Haghighatbin/LucidSens/Images/IMG_0358.jpg

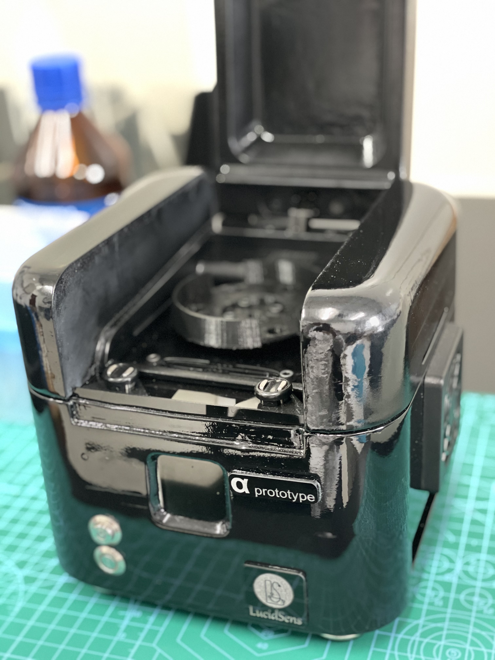
Images/IMG_0358.jpg
