Haghighatbin/LucidSens/Images/IMG_0595.jpg

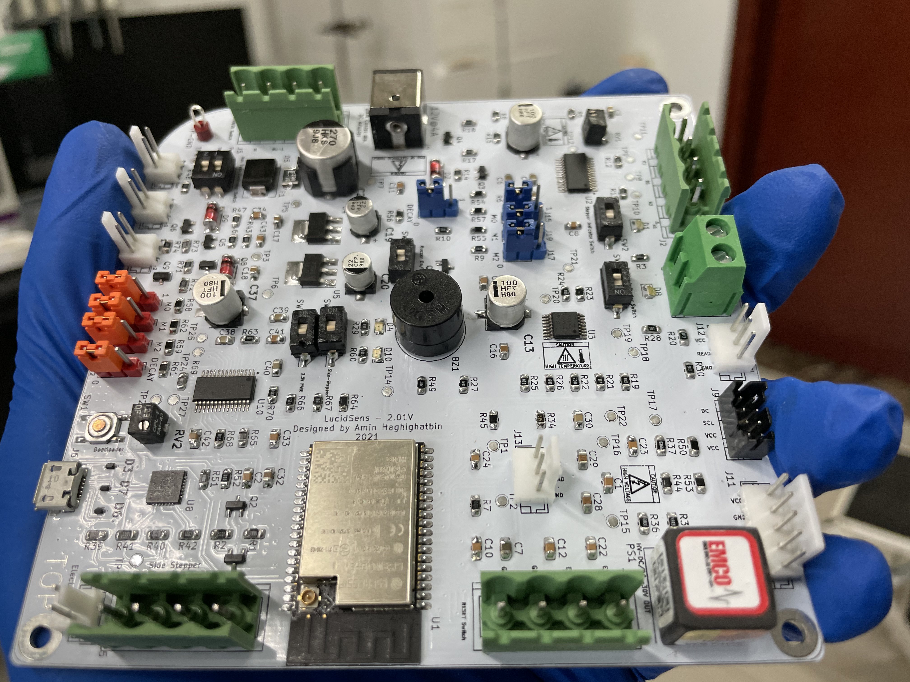
Images/IMG_0595.jpg
