Haghighatbin/LucidSens/Images/IMG_0702.JPG

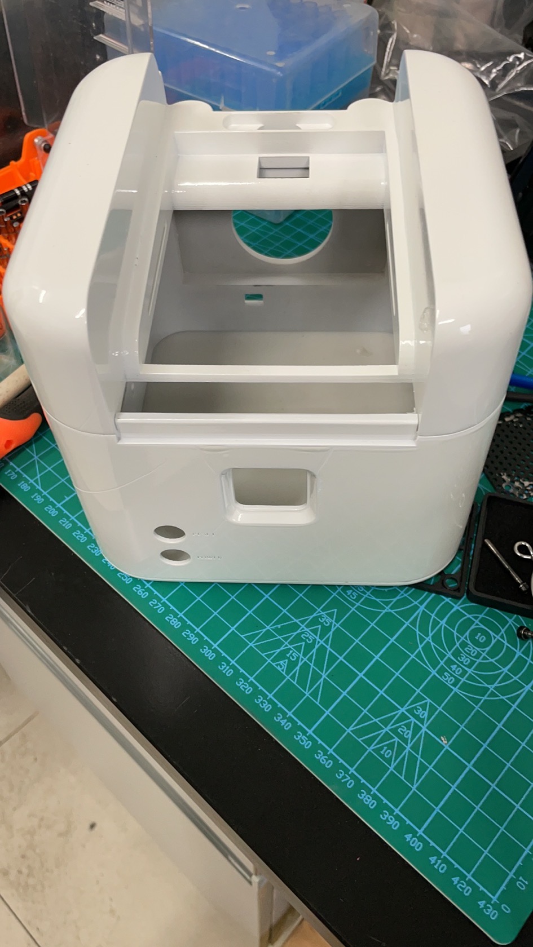
Images/IMG_0702.JPG
