Haghighatbin/LucidSens/Images/IMG_0709.jpg

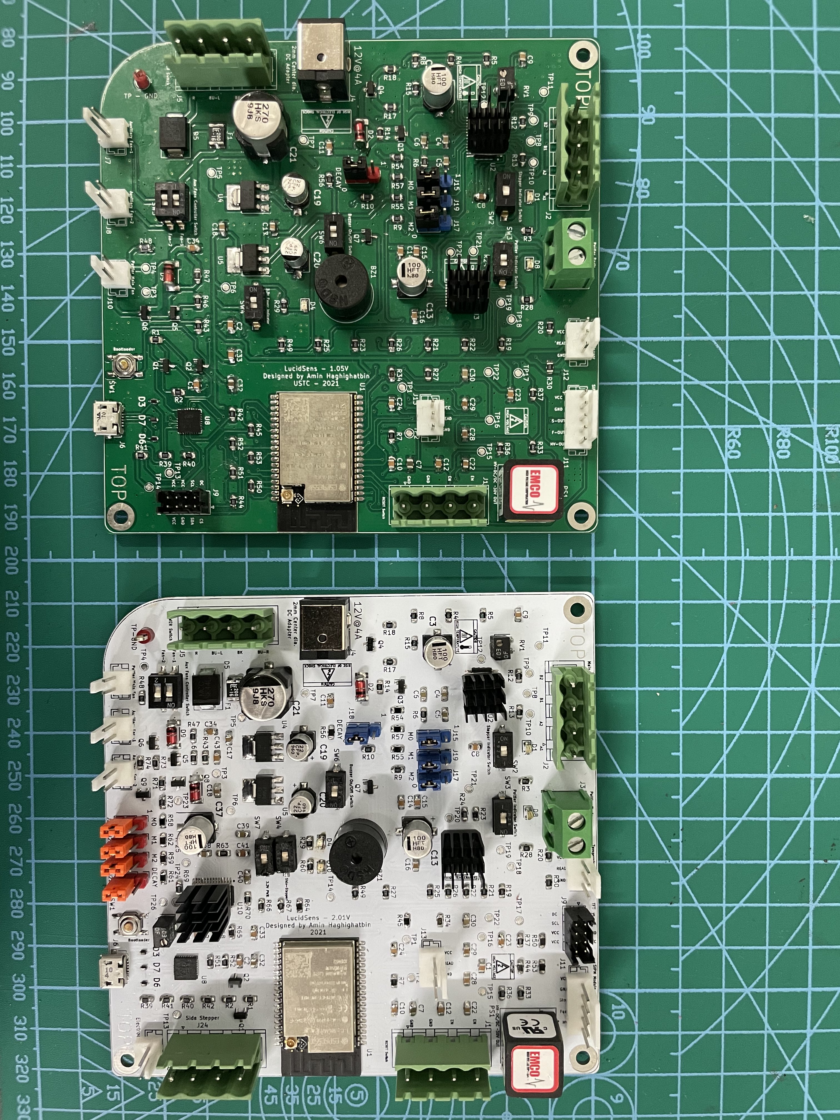
Images/IMG_0709.jpg
