Haghighatbin/LucidSens/Images/IMG_0712.jpg

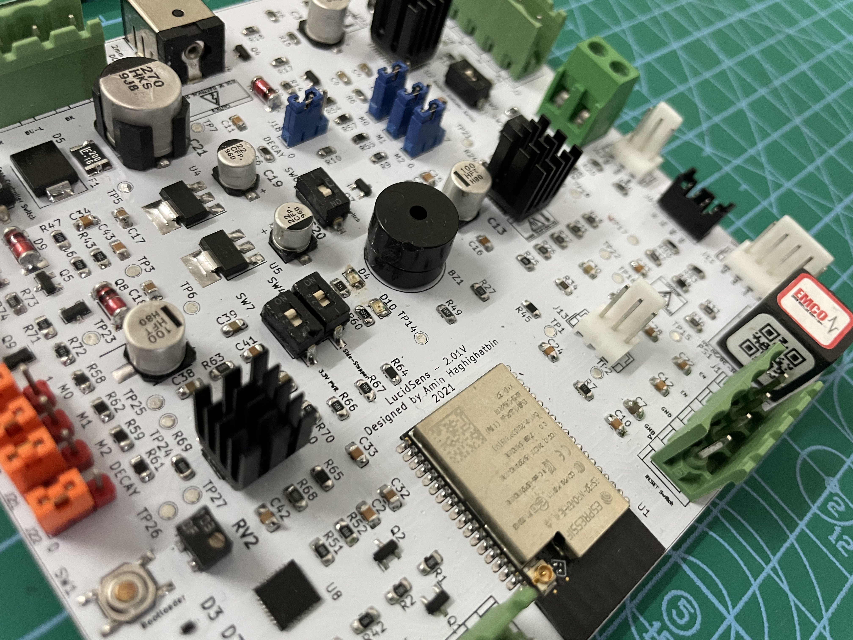
Images/IMG_0712.jpg
