Haghighatbin/LucidSens/Images/IMG_0715.jpg

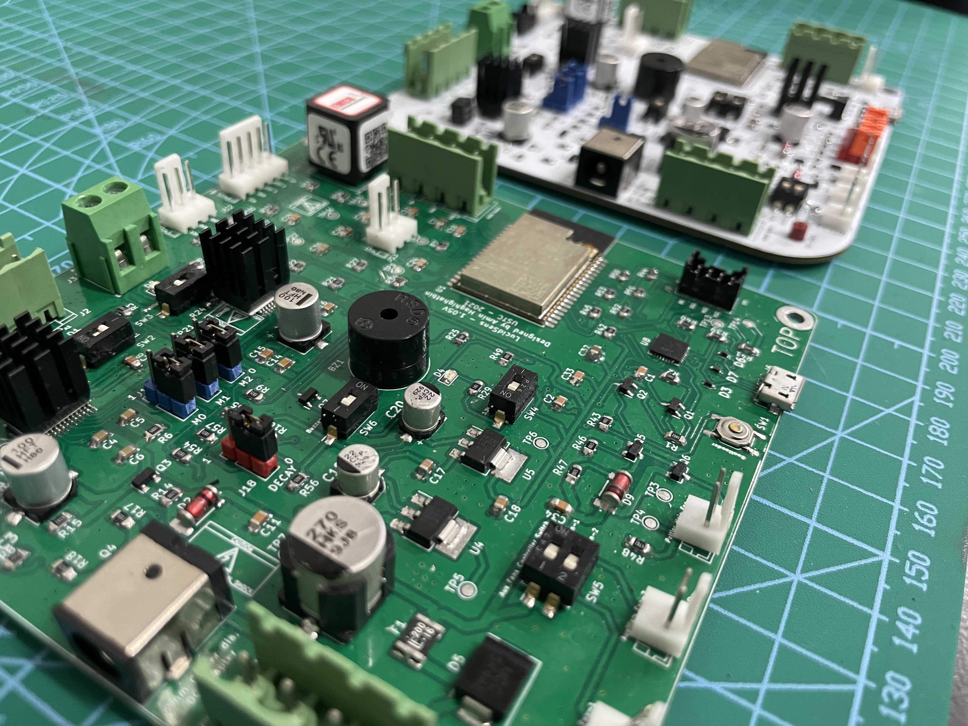
Images/IMG_0715.jpg
