Haghighatbin/LucidSens/Images/IMG_2450.jpg

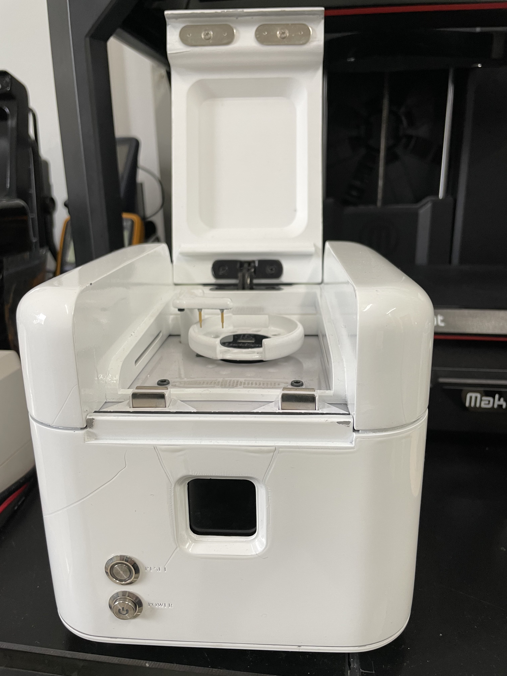
Images/IMG_2450.jpg
