Haghighatbin/LucidSens/Images/IMG_2451.jpg

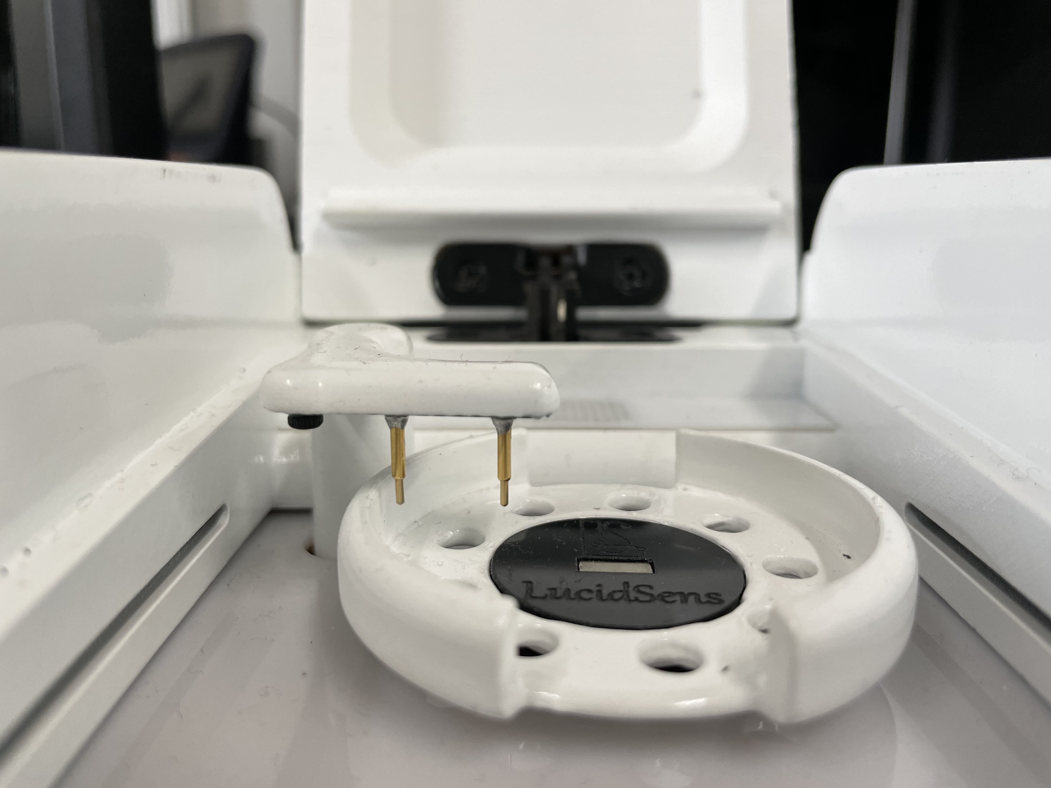
Images/IMG_2451.jpg
