Haghighatbin/LucidSens/Images/IMG_2452.jpg

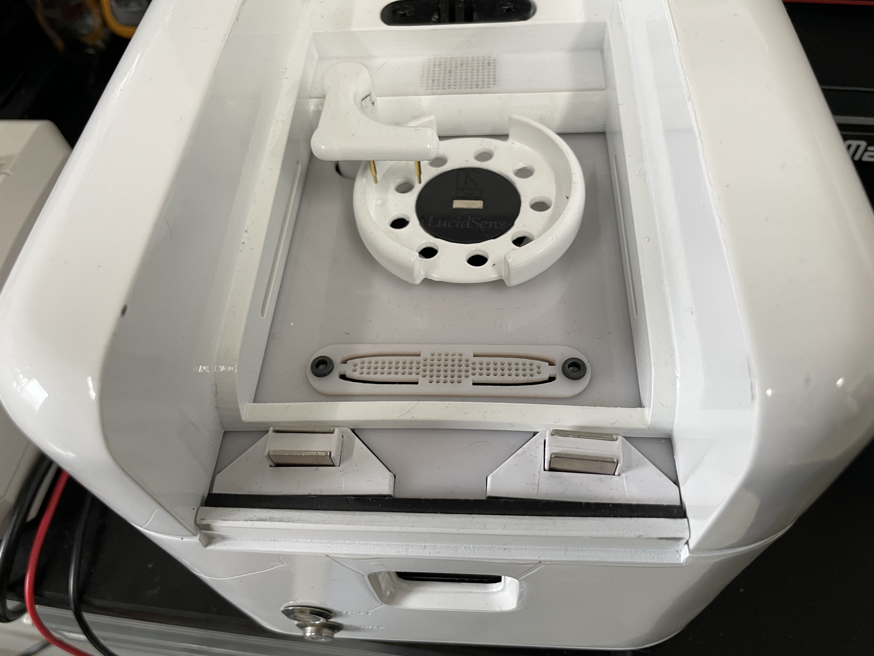
Images/IMG_2452.jpg
