Haghighatbin/LucidSens/Images/IMG_2453.jpg

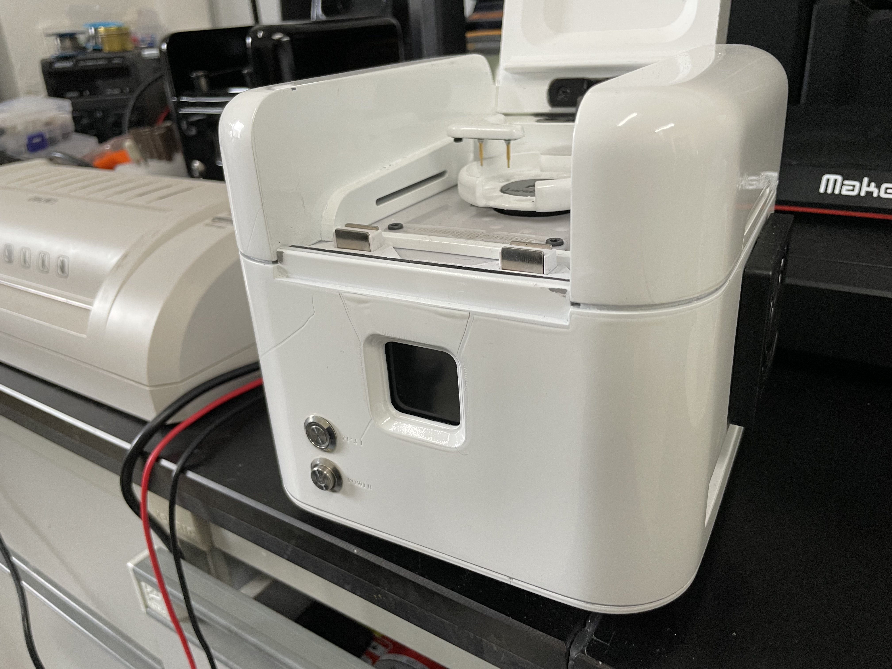
Images/IMG_2453.jpg
