Haghighatbin/LucidSens/Images/IMG_2455.jpg

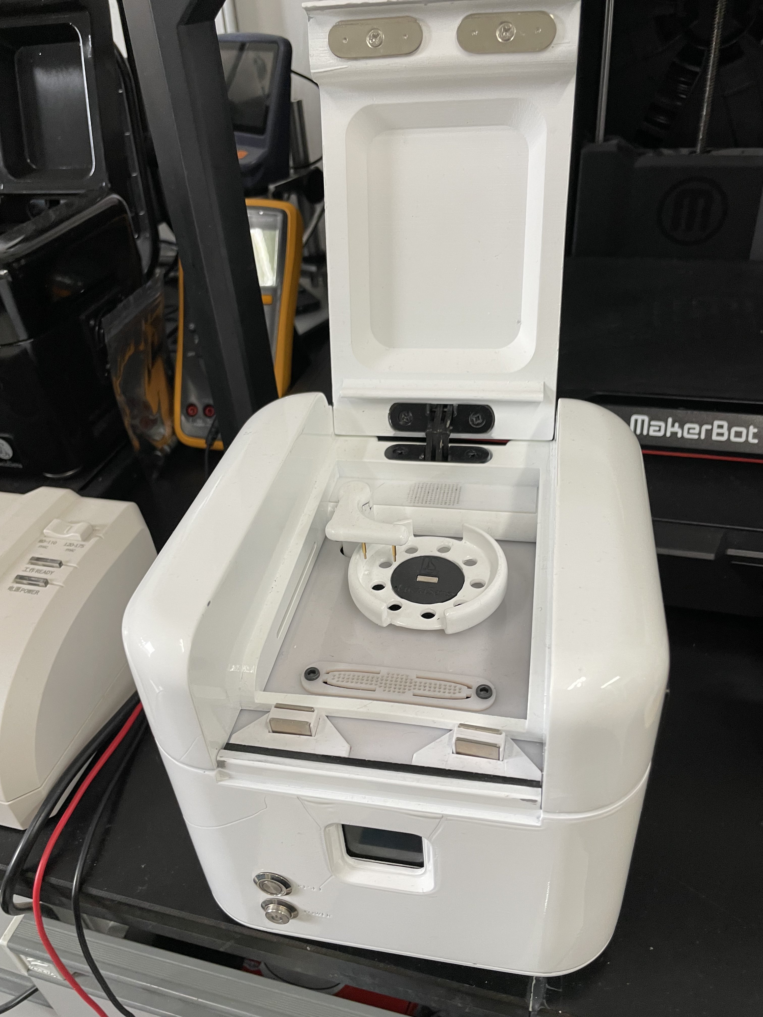
Images/IMG_2455.jpg
