Haghighatbin/LucidSens/Images/IMG_2456.jpg

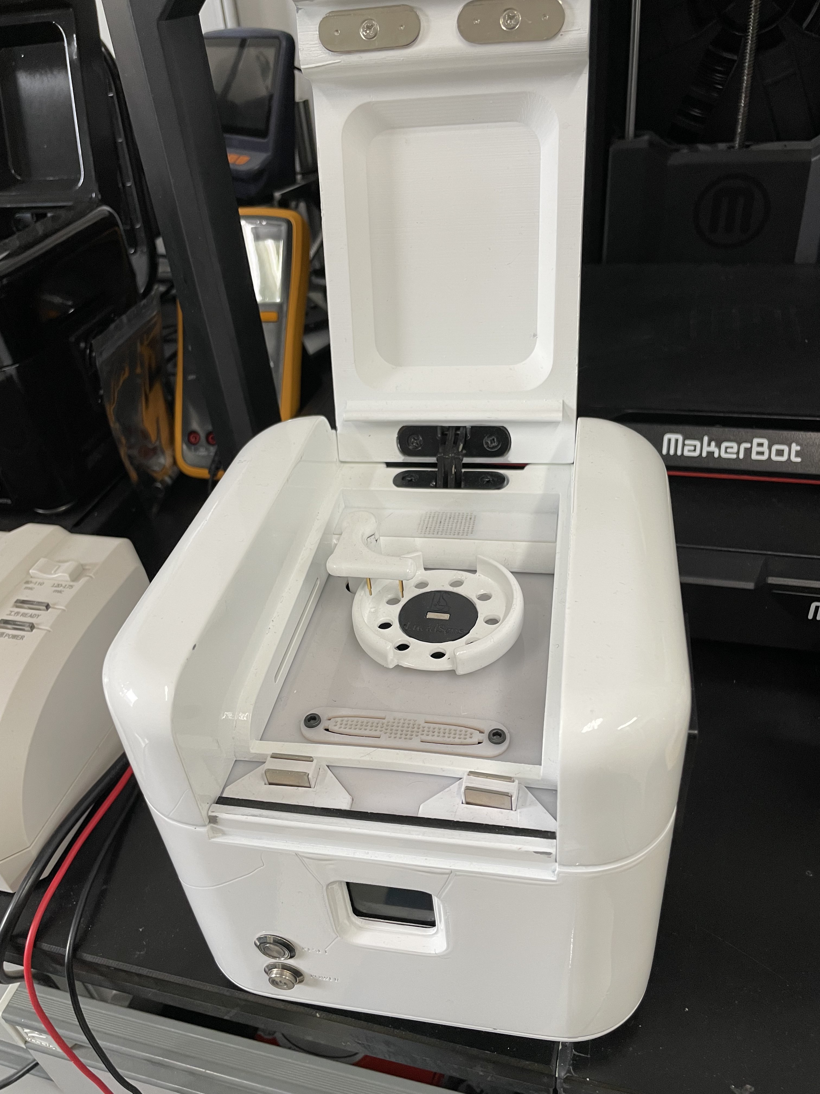
Images/IMG_2456.jpg
