Haghighatbin/LucidSens/Images/IMG_2458.jpg

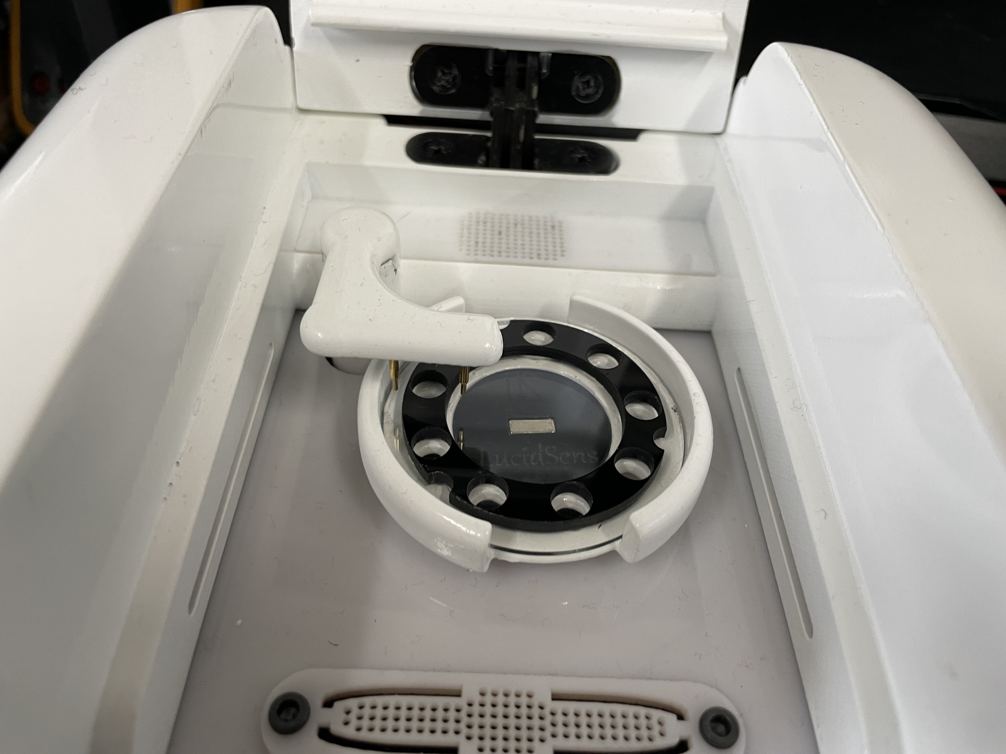
Images/IMG_2458.jpg
