Haghighatbin/LucidSens/Images/IMG_2459.jpg

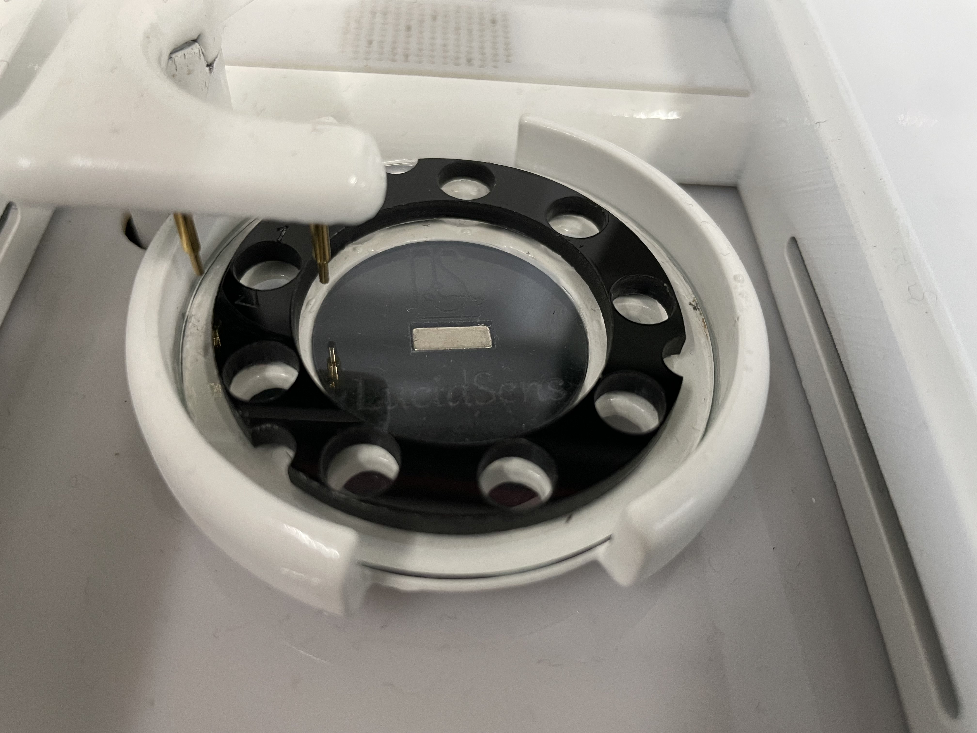
Images/IMG_2459.jpg
