Haghighatbin/LucidSens/Images/IMG_2460.jpg

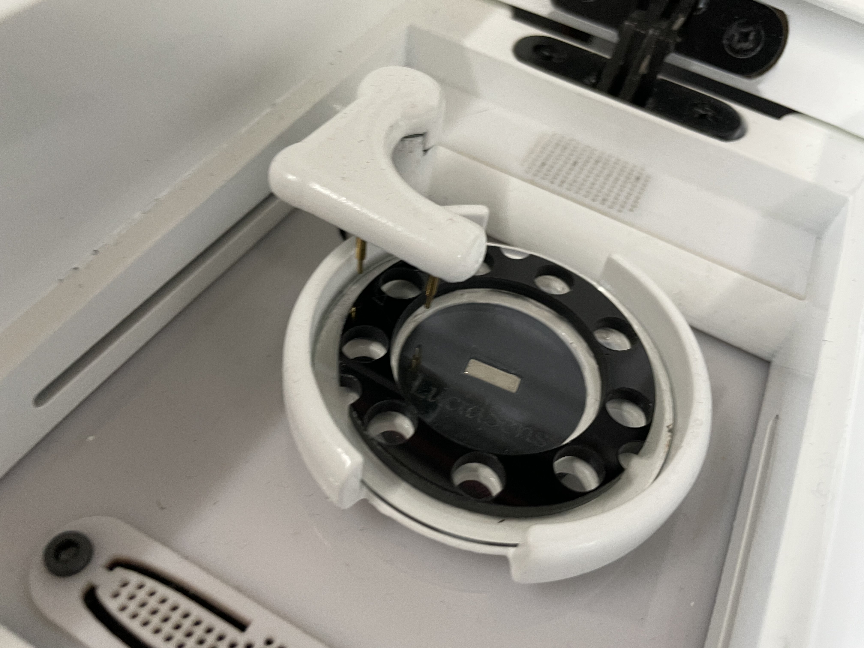
Images/IMG_2460.jpg
