Haghighatbin/LucidSens/Images/IMG_2461.jpg

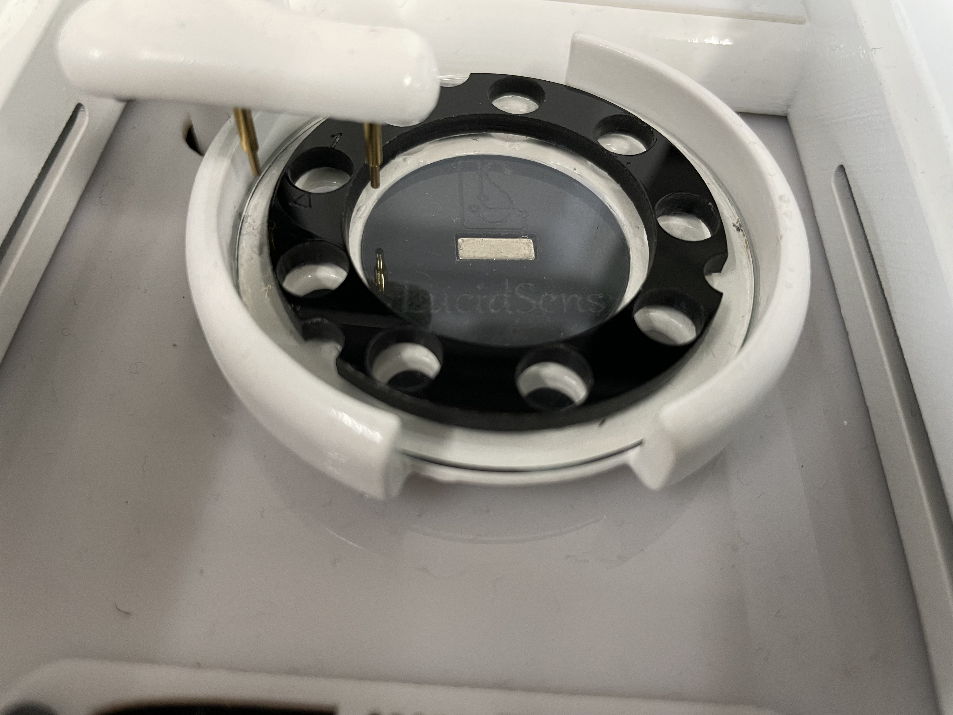
Images/IMG_2461.jpg
