Haghighatbin/LucidSens/Images/IMG_2462.jpg

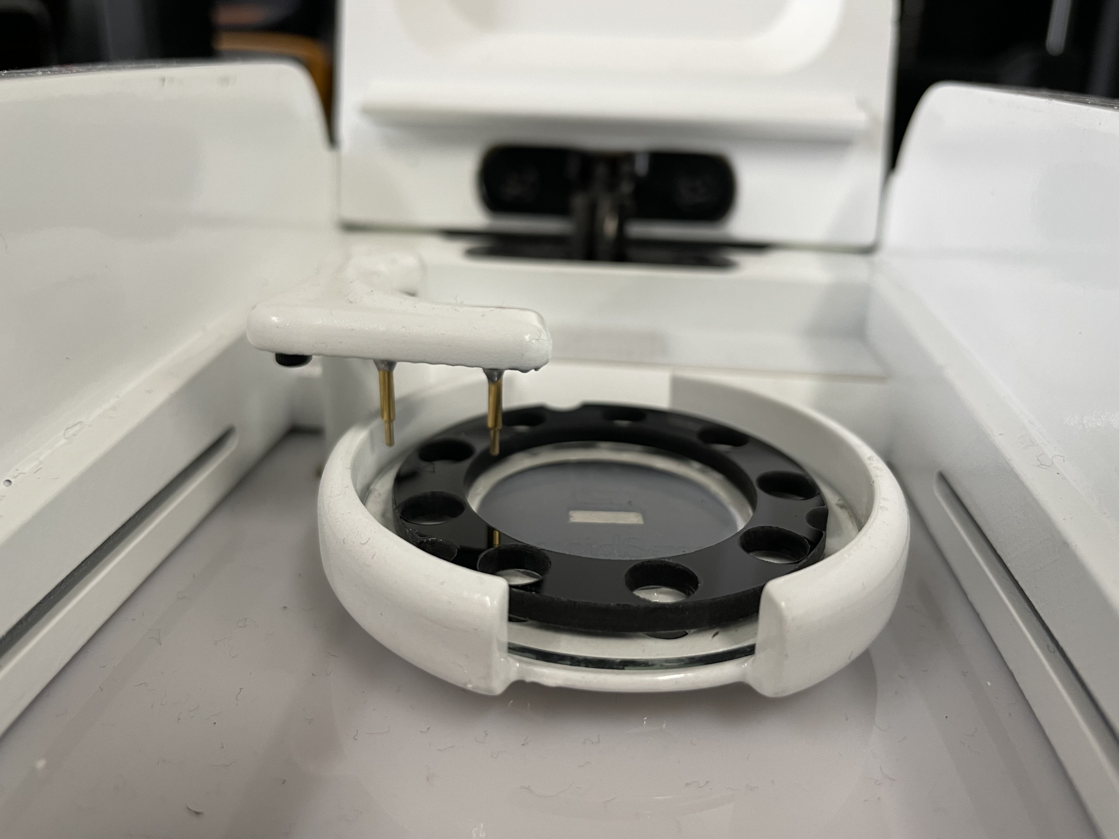
Images/IMG_2462.jpg
