Haghighatbin/LucidSens/Images/IMG_2463.jpg

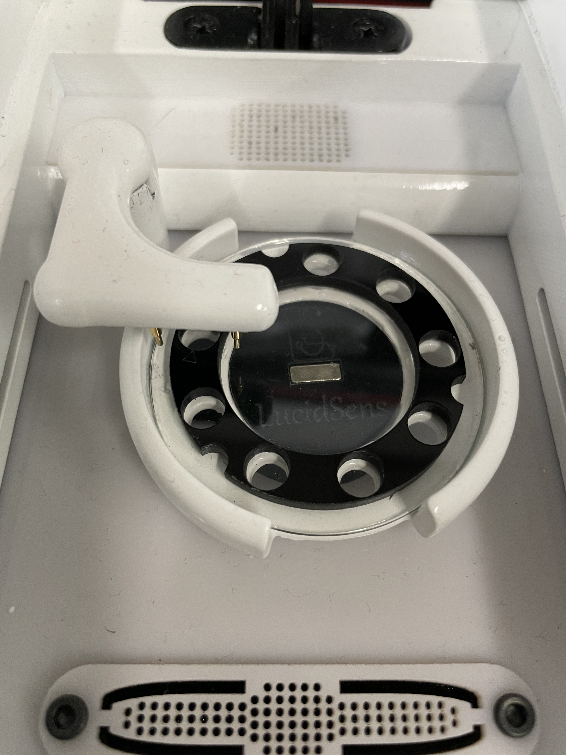
Images/IMG_2463.jpg
