Haghighatbin/LucidSens/Images/IMG_2464.jpg

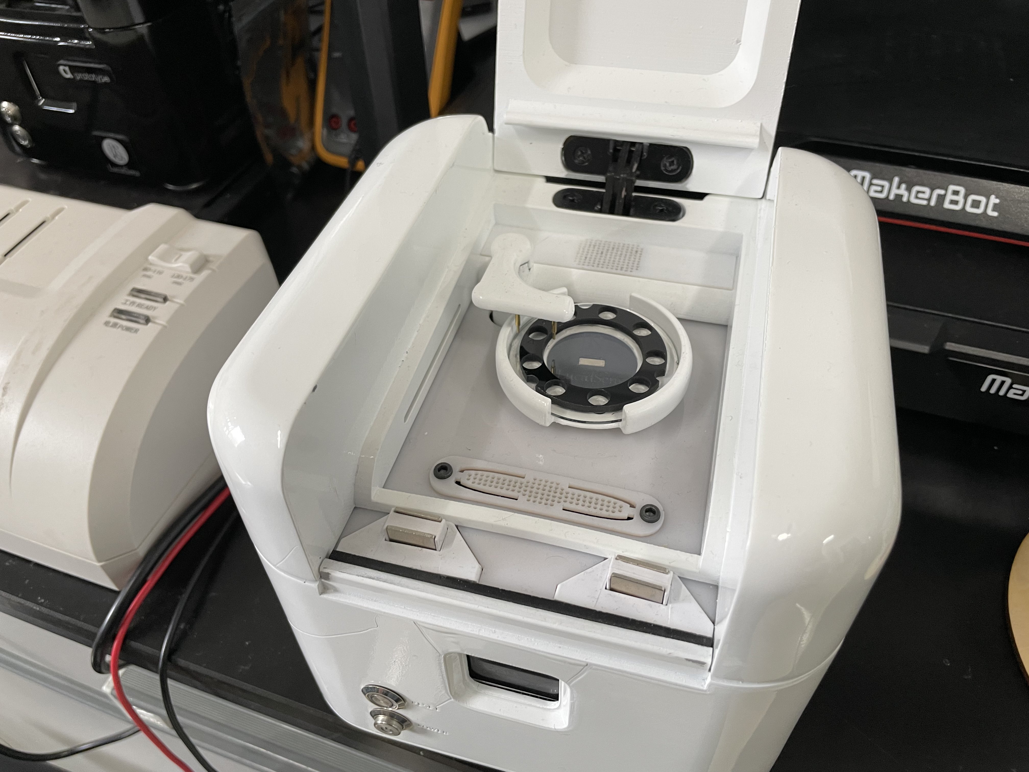
Images/IMG_2464.jpg
