Haghighatbin/LucidSens/Images/IMG_2465.jpg

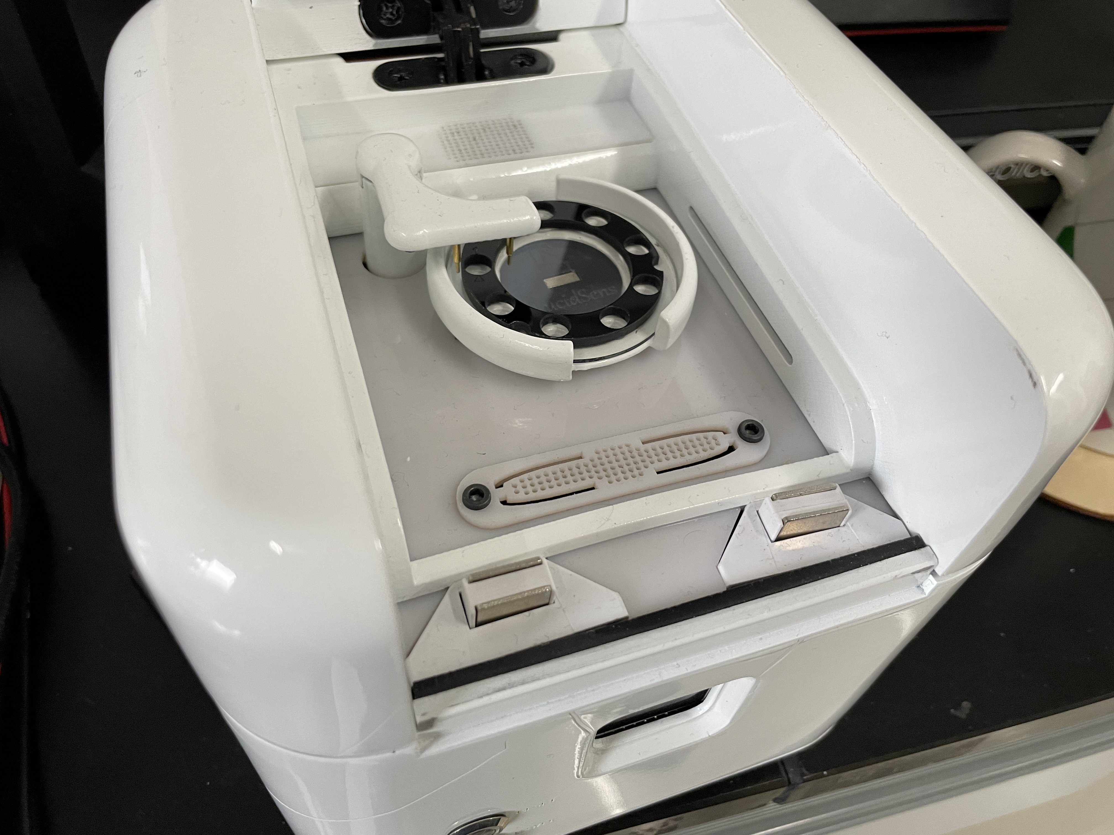
Images/IMG_2465.jpg
