Haghighatbin/LucidSens/Images/IMG_2466.jpg

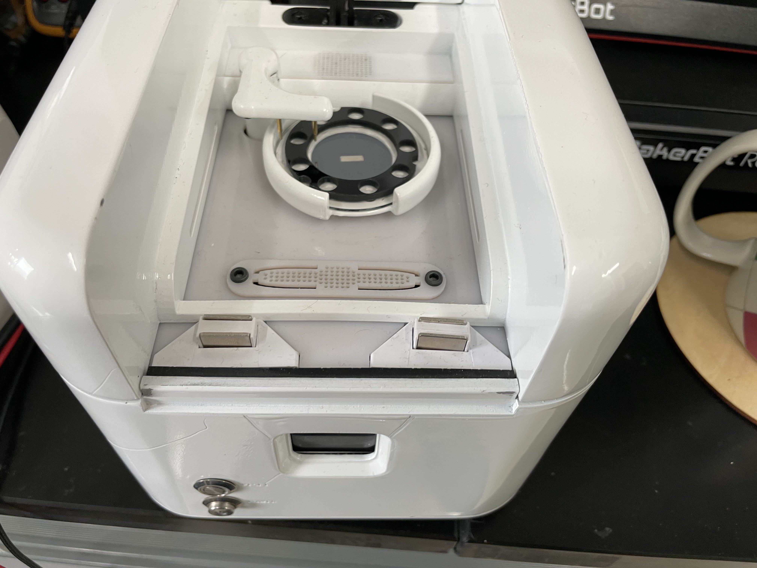
Images/IMG_2466.jpg
