Haghighatbin/LucidSens/Images/IMG_2468.jpg

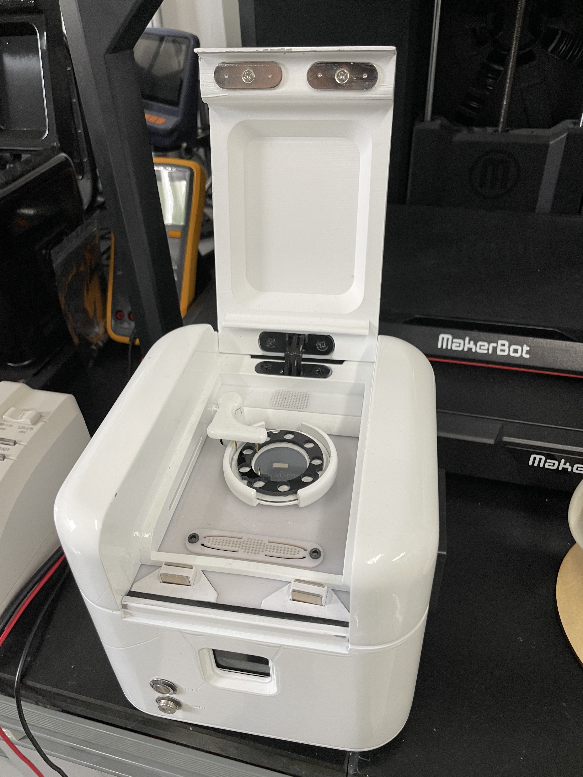
Images/IMG_2468.jpg
