Haghighatbin/LucidSens/Images/IMG_2470.jpg

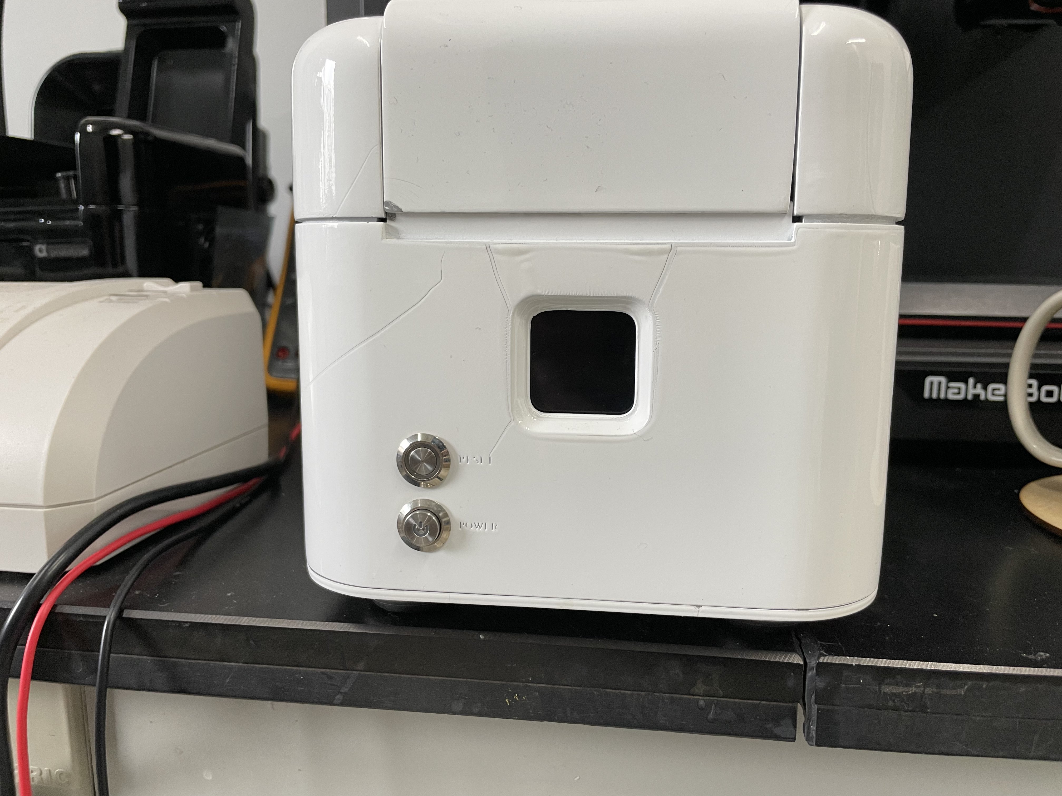
Images/IMG_2470.jpg
