Haghighatbin/LucidSens/Images/IMG_2471.jpg

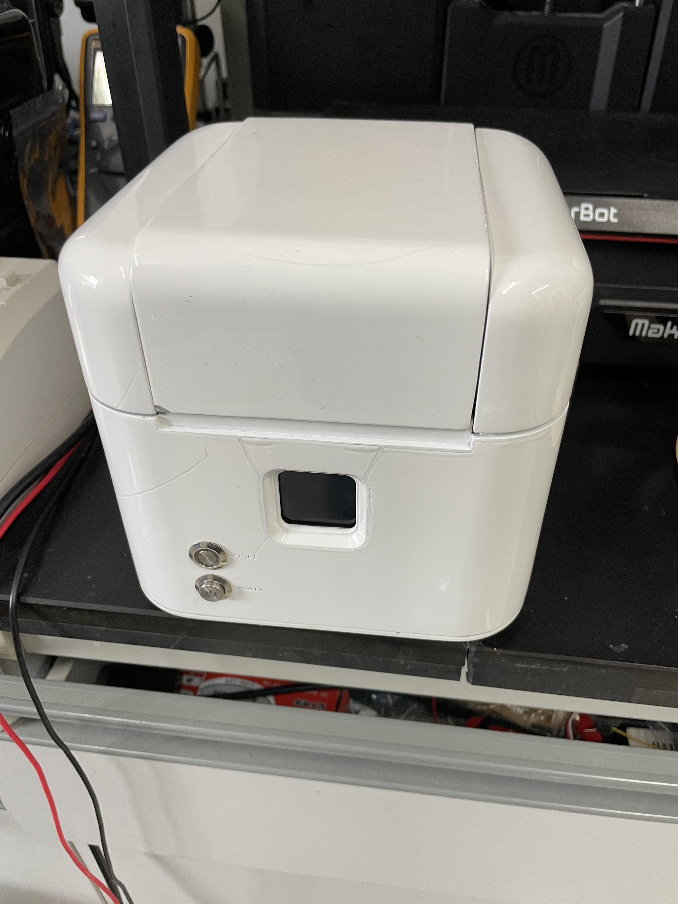
Images/IMG_2471.jpg
