Haghighatbin/LucidSens/Images/IMG_2472.jpg

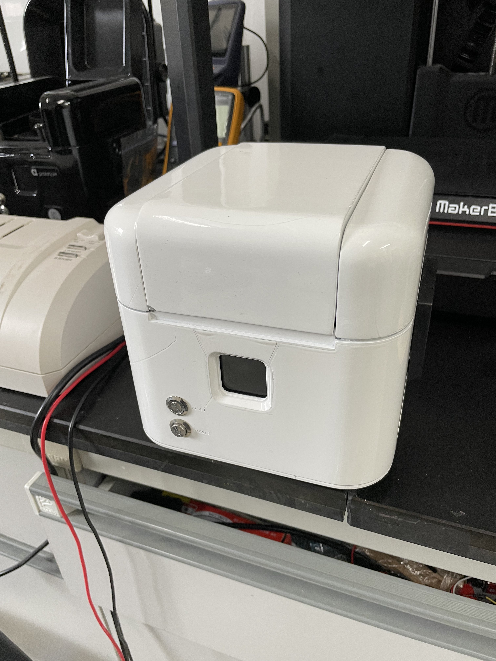
Images/IMG_2472.jpg
