Haghighatbin/LucidSens/Images/IMG_2476.jpg

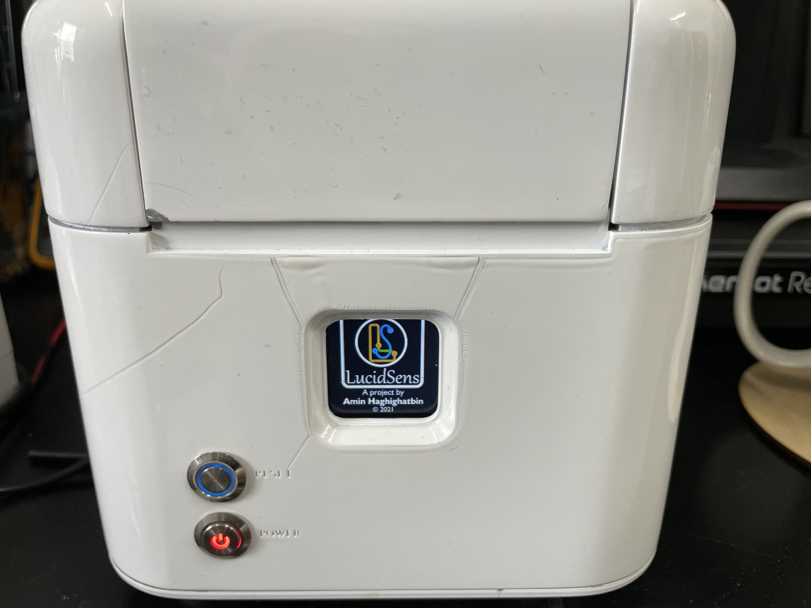
Images/IMG_2476.jpg
