Haghighatbin/LucidSens/Images/IMG_2478.jpg

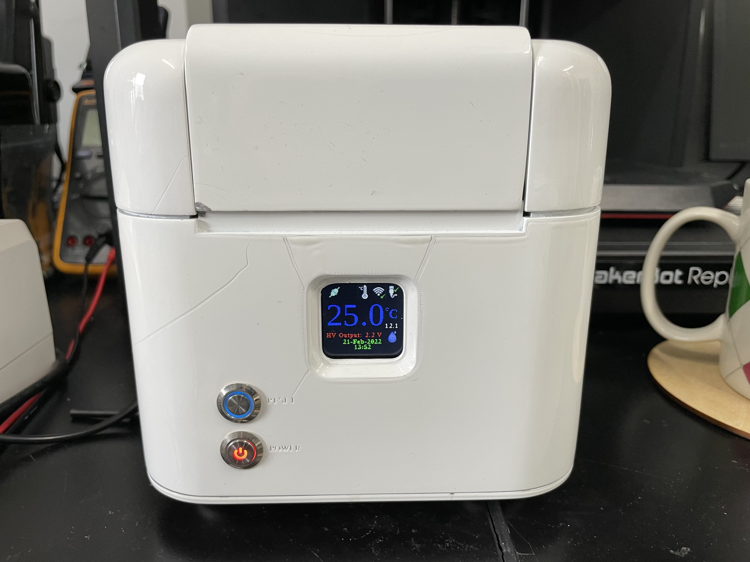
Images/IMG_2478.jpg
