Haghighatbin/LucidSens/Images/IMG_5526.JPG

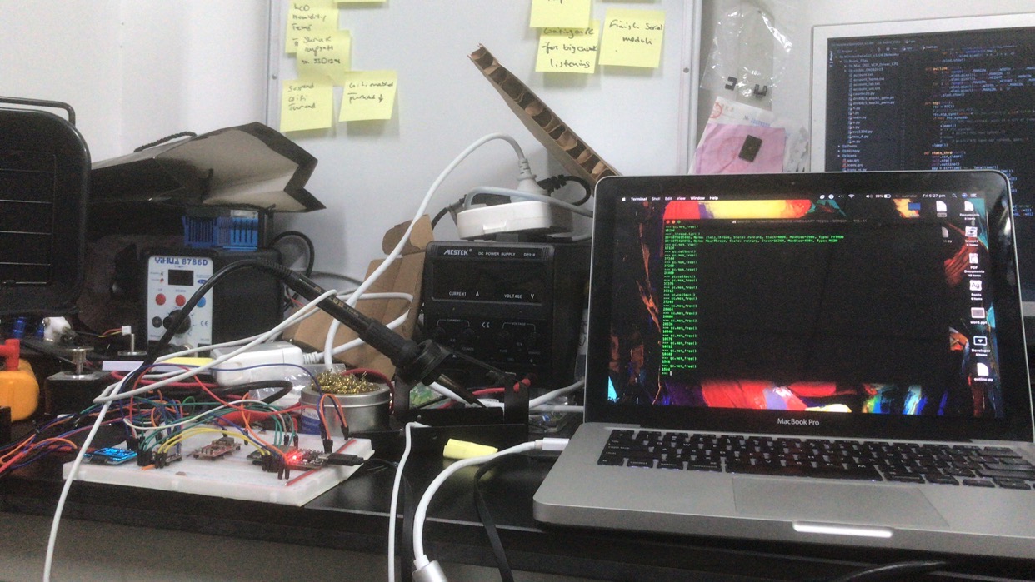
Images/IMG_5526.JPG
