Haghighatbin/LucidSens/Images/IMG_7764.jpg

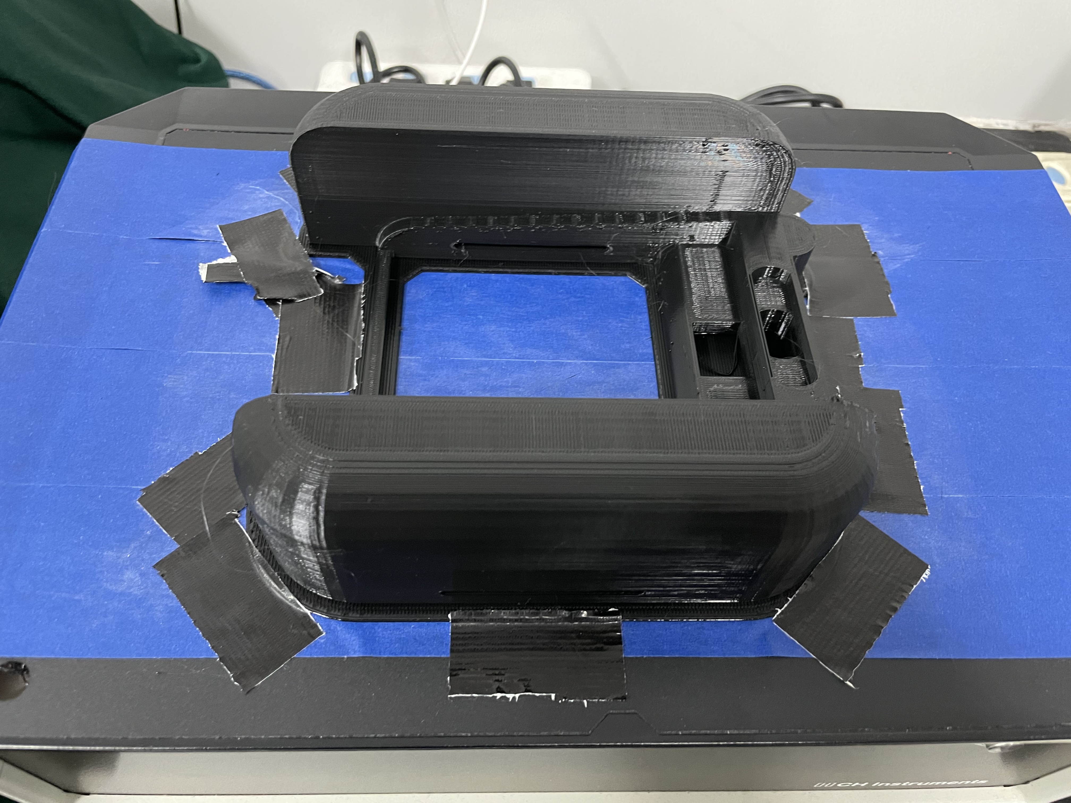
Images/IMG_7764.jpg
