Haghighatbin/LucidSens/Images/IMG_7788.jpg

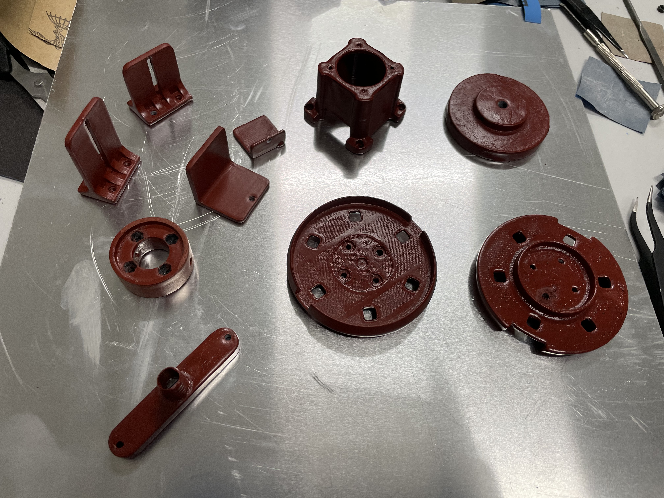
Images/IMG_7788.jpg
