Haghighatbin/LucidSens/Images/IMG_7793.jpg

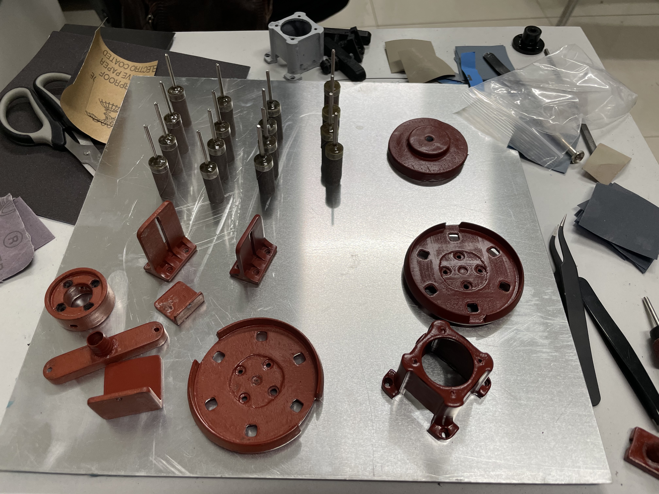
Images/IMG_7793.jpg
