Haghighatbin/LucidSens/Images/IMG_7794.jpg

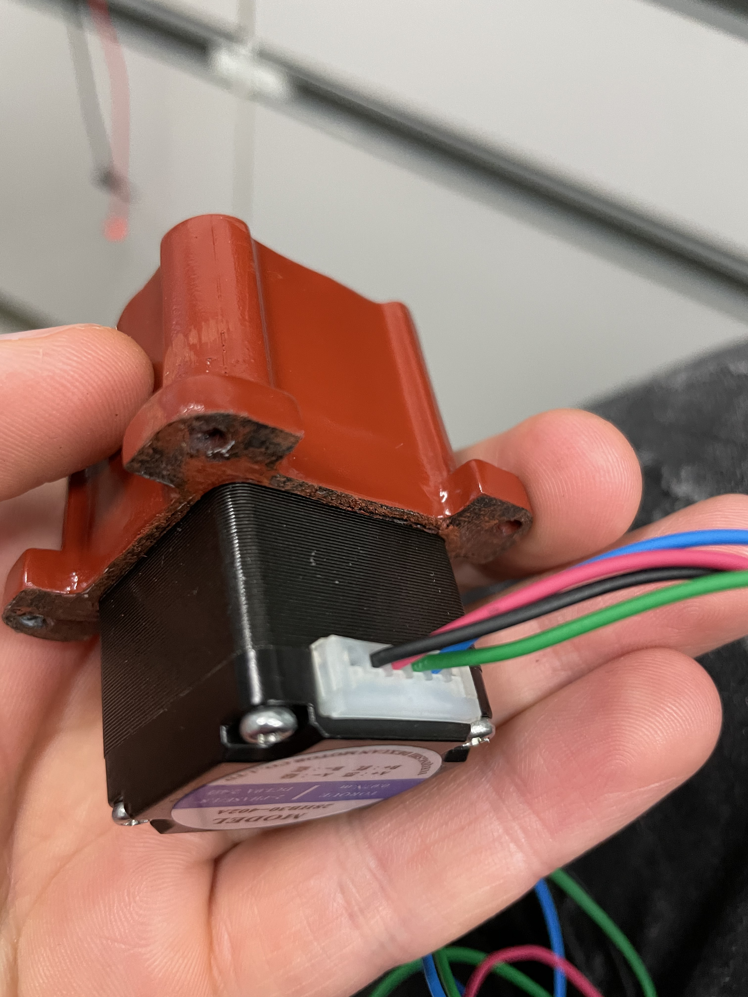
Images/IMG_7794.jpg
