Haghighatbin/LucidSens/Images/IMG_7806.jpg

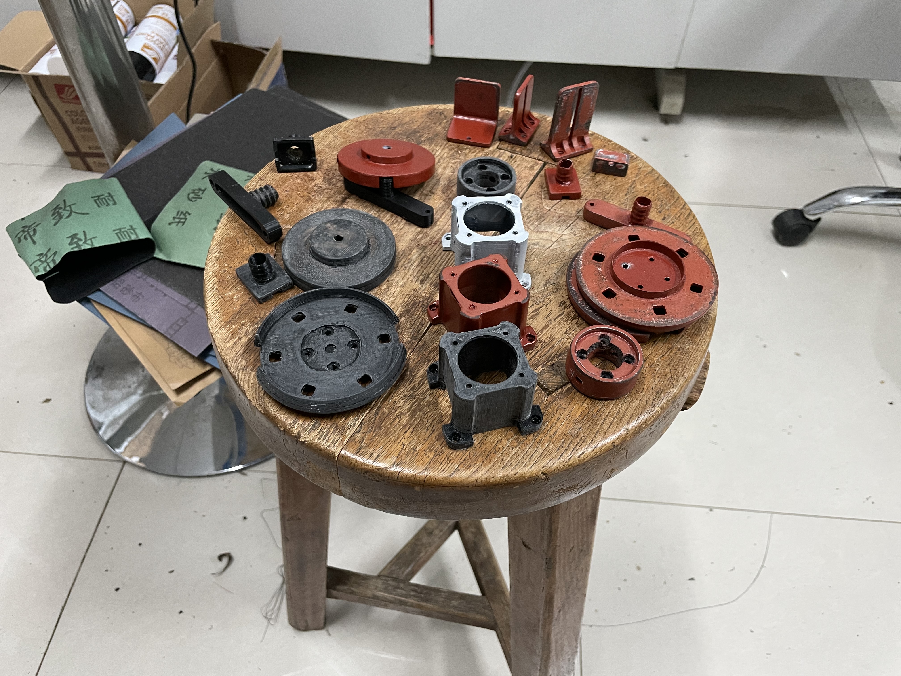
Images/IMG_7806.jpg
