Haghighatbin/LucidSens/Images/IMG_7807.jpg

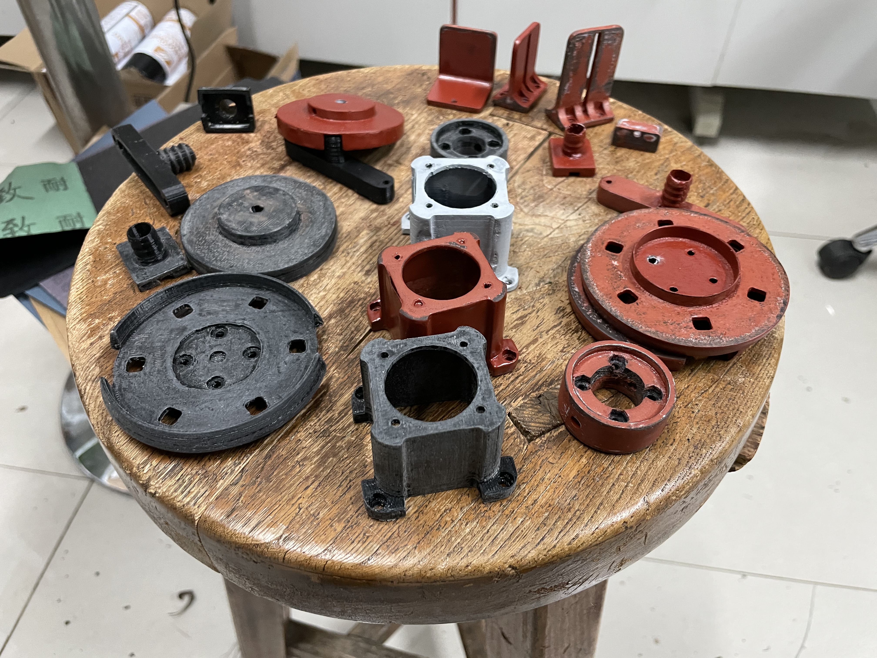
Images/IMG_7807.jpg
