Haghighatbin/LucidSens/Images/IMG_8523.jpg

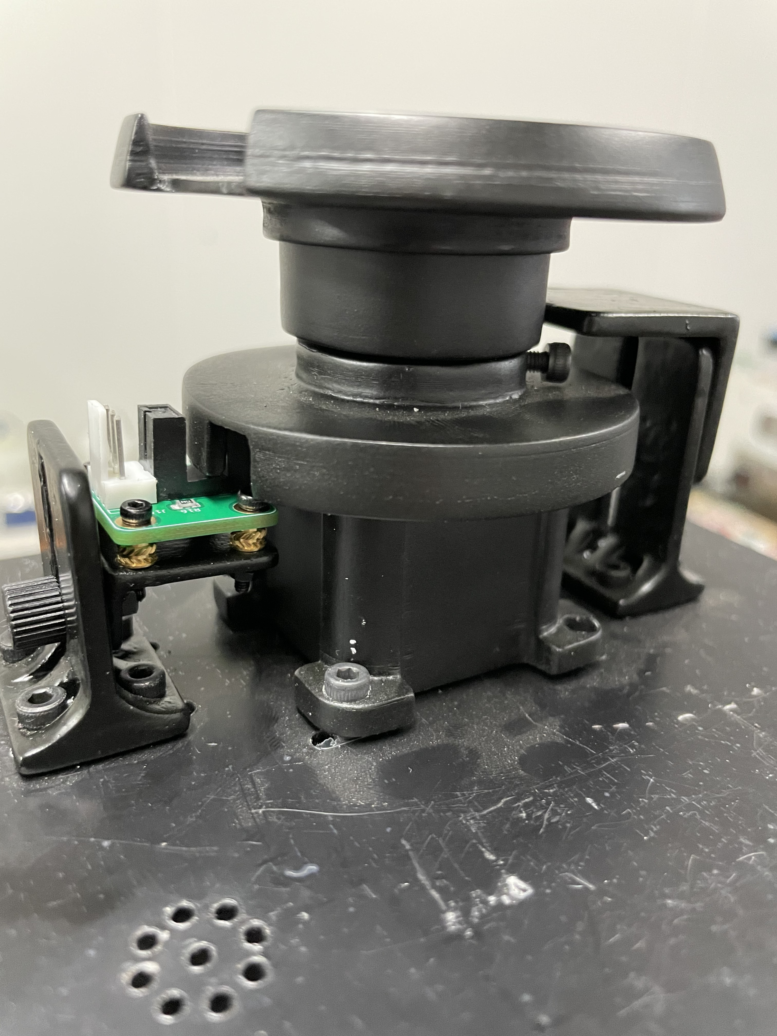
Images/IMG_8523.jpg
