Haghighatbin/LucidSens/Images/IMG_8666.jpg

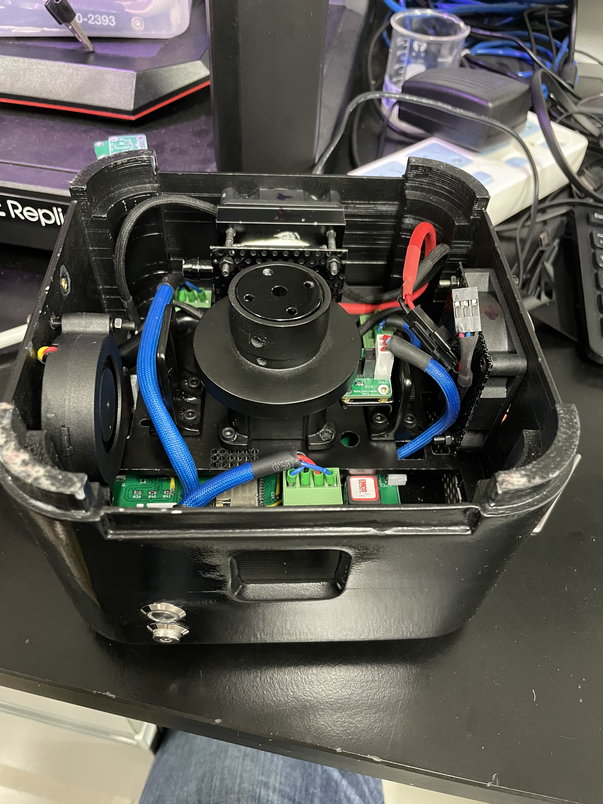
Images/IMG_8666.jpg
