Haghighatbin/LucidSens/Images/IMG_8667.jpg

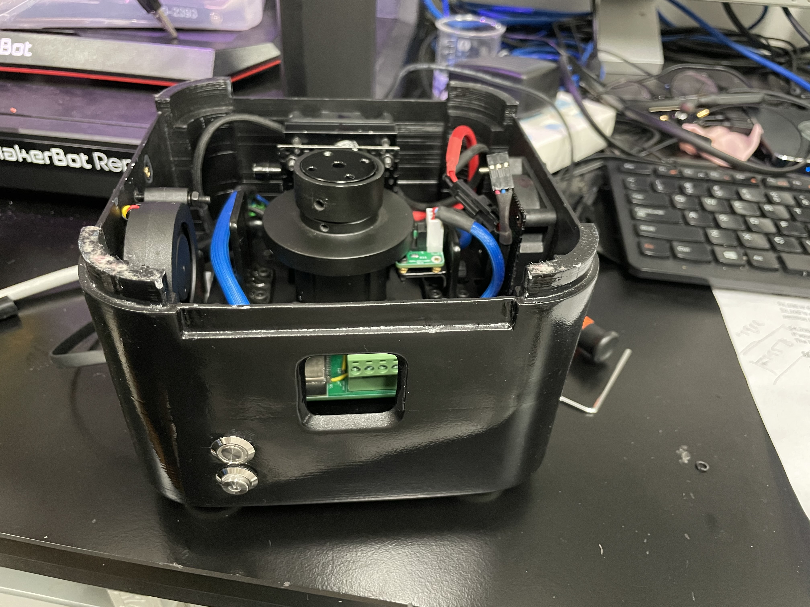
Images/IMG_8667.jpg
