Haghighatbin/LucidSens/Images/IMG_8668.jpg

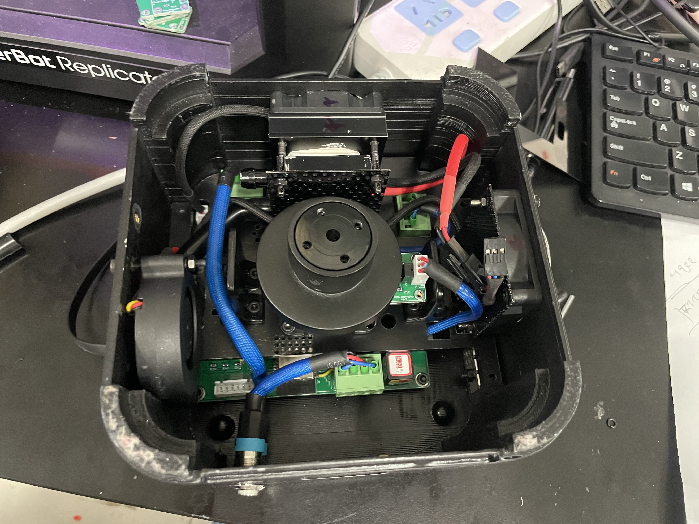
Images/IMG_8668.jpg
