Haghighatbin/LucidSens/Images/IMG_8669.jpg

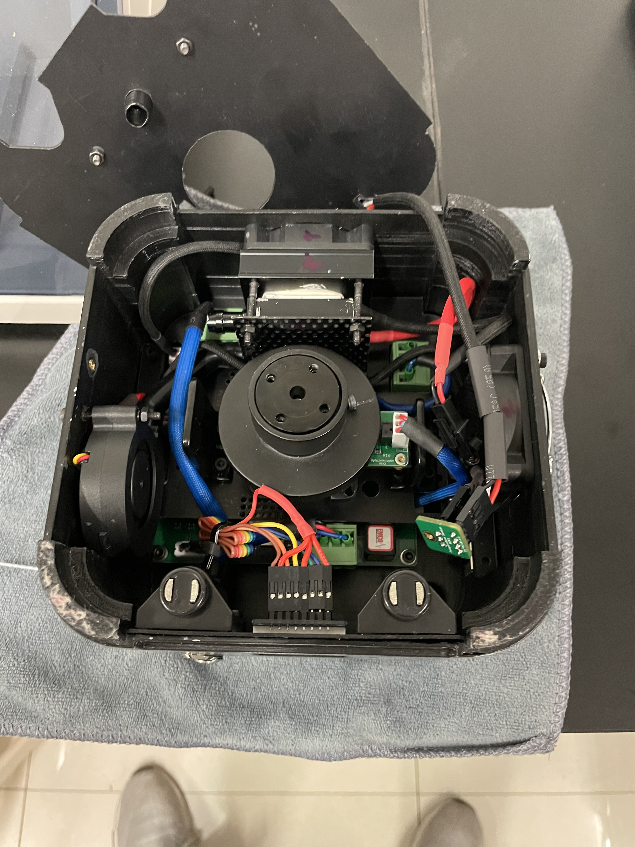
Images/IMG_8669.jpg
