Haghighatbin/LucidSens/Images/IMG_8670.jpg

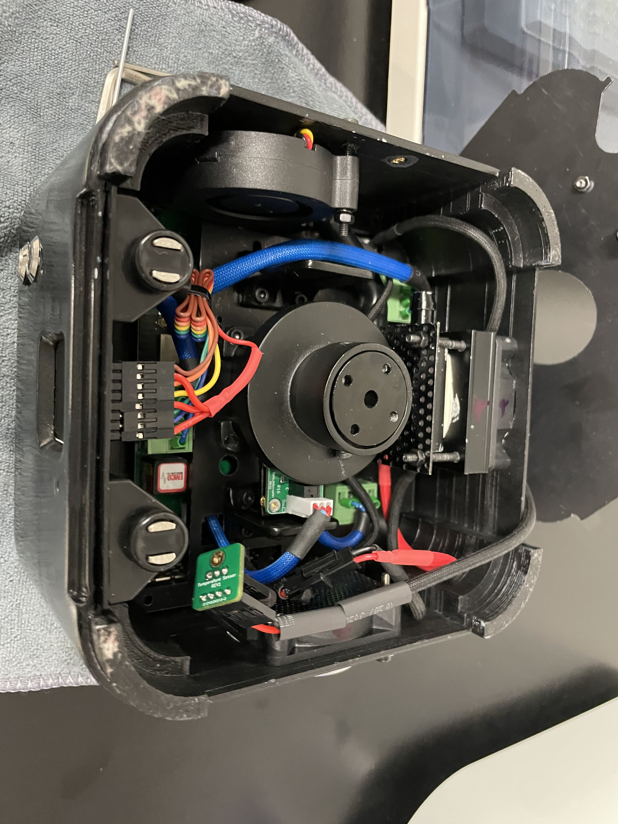
Images/IMG_8670.jpg
