Haghighatbin/LucidSens/Images/IMG_8677.jpg

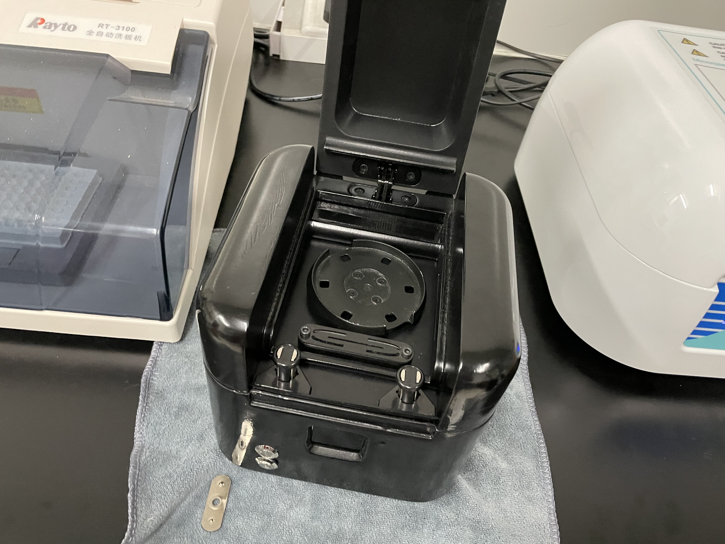
Images/IMG_8677.jpg
