Haghighatbin/LucidSens/Images/IMG_8678.jpg

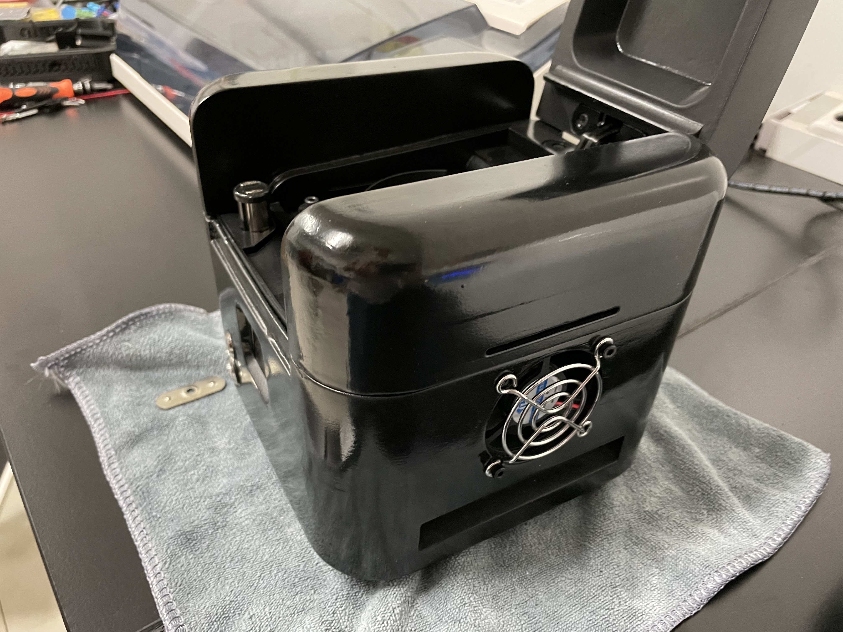
Images/IMG_8678.jpg
