Haghighatbin/LucidSens/Images/IMG_9771.JPG

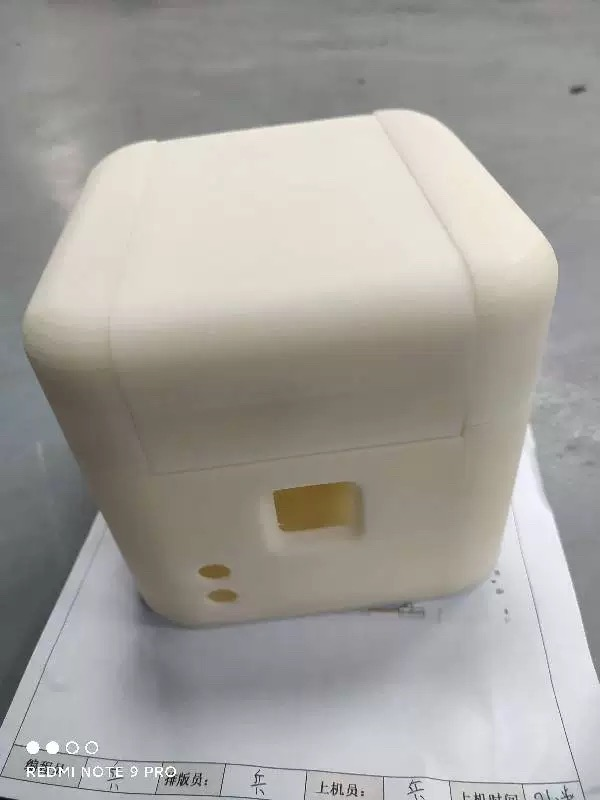
Images/IMG_9771.JPG
