Haghighatbin/LucidSens/Images/IMG_9930.JPG

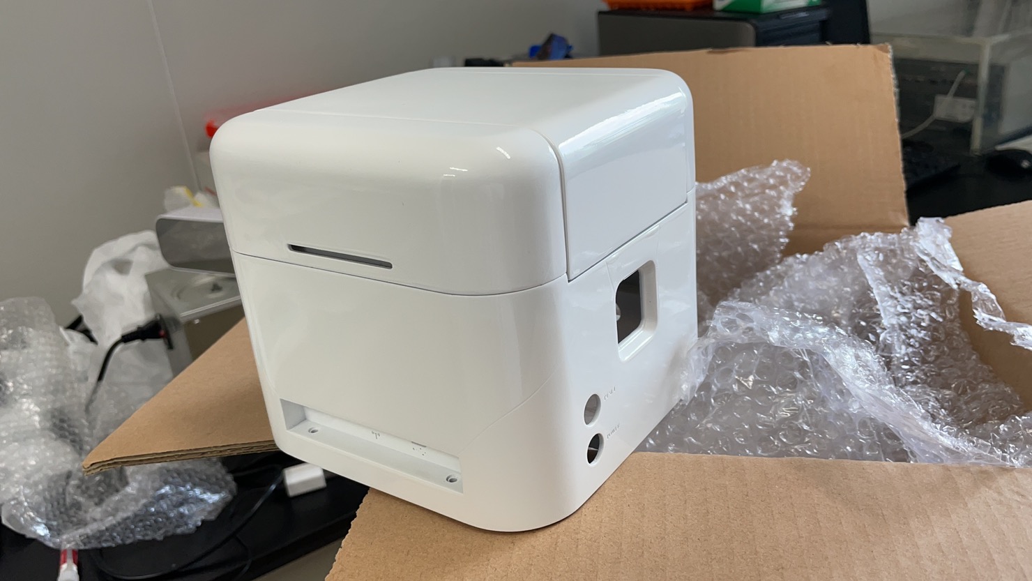
Images/IMG_9930.JPG
